frankyhub/Bike-Counter/pic/Shield-A.png

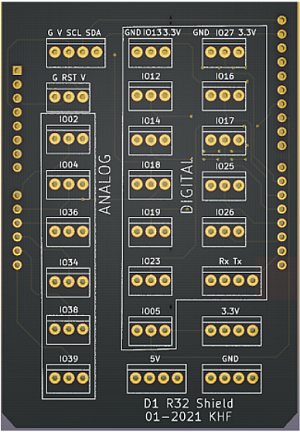
pic/Shield-A.png
